jblang/z80ctrl/firmware/emulation/bdos.c

/* z80ctrl (https://github.com/jblang/z80ctrl)
 * Copyright 2018-2023 J.B. Langston
 *
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
 * THE SOFTWARE IS PROVIDED "AS IS", WITHOUT WARRANTY OF ANY KIND, EXPRESS OR
 * IMPLIED, INCLUDING BUT NOT LIMITED TO THE WARRANTIES OF MERCHANTABILITY,
 * FITNESS FOR A PARTICULAR PURPOSE AND NONINFRINGEMENT. IN NO EVENT SHALL THE
 * AUTHORS OR COPYRIGHT HOLDERS BE LIABLE FOR ANY CLAIM, DAMAGES OR OTHER
 * LIABILITY, WHETHER IN AN ACTION OF CONTRACT, TORT OR OTHERWISE, ARISING
 * FROM, OUT OF OR IN CONNECTION WITH THE SOFTWARE OR THE USE OR OTHER
 * DEALINGS IN THE SOFTWARE.
 */

/*
 * Credit to RunCPM https://github.com/MockbaTheBorg/RunCPM for showing me
 * that emulating BDOS on a FAT filesystem was possible, and for serving as
 * a sanity check to help me understand BDOS behavior when I wasn't sure
 * from reading the BDOS assembly code.  No code has been copied though.
 */

/**
 * @file bdos.c BDOS disk emulation on FatFS
 */

#include <ctype.h>
#include <stdint.h>
#include <stdio.h>
#include <string.h>

#include "fatfs/ff.h"

#include "hardware/io.h"
#include "hardware/memory.h"
#include "hardware/timer.h"

#include "util/ffwrap.h"
#include "util/pgmspace.h"
#include "util/string.h"

#include "bdos.h"

// Uncomment for debug messages

// CP/M constants
#define RECSIZ 128L // # of bytes in a record (rc)
#define RECCNT 128L // Max # of records in an extent
#define EXTSIZ (RECSIZ * RECCNT) // # of bytes in an extent (ex)
#define EXTCNT 32L // Max # of extents in a module
#define MODSIZ (EXTSIZ * EXTCNT) // # of bytes in a module (s2)
#define MODCNT 16L // Max # of modules in a file
#define DEFFCB 0x5c // Default FCB location
#define DEFDMA 0x80 // Default DMA buffer

// BDOS function calls
enum {
    P_TERMCPM = 0,
    C_READ = 1,
    C_WRITE = 2,
    A_READ = 3,
    A_WRITE = 4,
    L_WRITE = 5,
    C_RAWIO = 6,
    C_GETIOB = 7,
    C_SETIOB = 8,
    C_WRITESTR = 9,
    C_READSTR = 10,
    C_STAT = 11,
    S_BDOSVER = 12,
    DRV_ALLRESET = 13,
    DRV_SET = 14,
    F_OPEN = 15,
    F_CLOSE = 16,
    F_SFIRST = 17,
    F_SNEXT = 18,
    F_DELETE = 19,
    F_READ = 20,
    F_WRITE = 21,
    F_MAKE = 22,
    F_RENAME = 23,
    DRV_LOGINVEC = 24,
    DRV_GET = 25,
    F_DMAOFF = 26,
    DRV_ALLOCVEC = 27,
    DRV_SETRO = 28,
    DRV_ROVEC = 29,
    F_ATTRIB = 30,
    DRV_DPB = 31,
    F_USERNUM = 32,
    F_READRAND = 33,
    F_WRITERAND = 34,
    F_SIZE = 35,
    F_RANDREC = 36,
    DRV_RESET = 37,
    DRV_ACCESS = 38,
    DRV_FREE = 39,
    F_WRITEZF = 40
};

const char bdos_names[] PROGMEM =
    "P_TERMCPM\0"
    "C_READ\0"
    "C_WRITE\0"
    "A_READ\0"
    "A_WRITE\0"
    "L_WRITE\0"
    "C_RAWIO\0"
    "C_GETIOB\0"
    "C_SETIOB\0"
    "C_WRITESTR\0"
    "C_READSTR\0"
    "C_STAT\0"
    "S_BDOSVER\0"
    "DRV_ALLRESET\0"
    "DRV_SET\0"
    "F_OPEN\0"
    "F_CLOSE\0"
    "F_SFIRST\0"
    "F_SNEXT\0"
    "F_DELETE\0"
    "F_READ\0"
    "F_WRITE\0"
    "F_MAKE\0"
    "F_RENAME\0"
    "DRV_LOGINVEC\0"
    "DRV_GET\0"
    "F_DMAOFF\0"
    "DRV_ALLOCVEC\0"
    "DRV_SETRO\0"
    "DRV_ROVEC\0"
    "F_ATTRIB\0"
    "DRV_DPB\0"
    "F_USERNUM\0"
    "F_READRAND\0"
    "F_WRITERAND\0"
    "F_SIZE\0"
    "F_RANDREC\0"
    "DRV_RESET\0"
    "DRV_ACCESS\0"
    "DRV_FREE\0"
    "F_WRITEZF\0";

// BDOS return codes
enum {
    BDOS_SUCCESS = 0,
    BDOS_EOF = 1,
    BDOS_ERROR = 0xff
};

// FCB layout
typedef struct {
    uint8_t dr;
    uint8_t fn[11];
    uint8_t ex;
    uint8_t s1;
    uint8_t s2;
    uint8_t rc;
    uint8_t al[16];
    uint8_t cr;
    uint8_t r0, r1, r2;
} fcb_t;

typedef struct {
    uint8_t uu;
    uint8_t fn[11];
    uint8_t ex;
    uint8_t s1;
    uint8_t s2;
    uint8_t rc;
    uint16_t al[8];
} dir_t;

// Disk Parameter Block
typedef struct {
    uint16_t spt;
    uint8_t bsh;
    uint8_t blm;
    uint8_t exm;
    uint16_t dsm;
    uint16_t drm;
    uint8_t al0;
    uint8_t al1;
    uint16_t cks;
    uint16_t off;
} dpb_t;

// Parameter mailbox format
typedef struct {
    uint16_t fcbaddr;
    uint16_t ret;
    uint8_t curdrv;
    uint16_t dmaaddr;
    uint8_t usernum;
    uint16_t alloc;
    uint16_t rodsk;
    uint16_t dlog;
} bdos_mailbox_t;

static uint16_t dma_mailbox = 0;
static uint8_t dma_command = 0;
static dma_status_t dma_status = DMA_MAILBOX_UNSET;
static bdos_mailbox_t params;

uint8_t curfn[11]; // FCB filename of the currently open file
static fcb_t curfcb; // FCB for the current command
static FIL curfil;
static FILINFO curfno;

uint8_t bdos_debug = 0;

/**
 * Get null-terminated filename.ext from fixed length FCB field
 */
void fcb_fatname(uint8_t* fatname, uint8_t* fcbname)
{
    uint8_t j = 0;
    for (uint8_t i = 0; i < 11; i++) {
        if (i == 8)
            fatname[j++] = '.';
        if (fcbname[i] != ' ')
            fatname[j++] = toupper(fcbname[i] & 0x7f);
    }
    fatname[j] = '\0';
}

/**
 * Set fixed-length FCB field from null-terminated filename.ext
 */
void fcb_setname(uint8_t* fcbname, uint8_t* fatname)
{
    uint8_t i = 0, j = 0;
    while (i < 8)
        if (fatname[j] == '.' || fatname[j] == 0)
            fcbname[i++] = ' ';
        else if (fatname[j] == '*')
            fcbname[i++] = '?';
        else
            fcbname[i++] = toupper(fatname[j++] & 0x7f);
    while (fatname[j] == '*' || fatname[j] == '.')
        j++;
    while (i < 11)
        if (fatname[j] == 0)
            fcbname[i++] = ' ';
        else if (fatname[j] == '*')
            fcbname[i++] = '?';
        else
            fcbname[i++] = toupper(fatname[j++] & 0x7f);
}

/**
 * Parse d:filename.ext argument and set FCB fields
 */
void fcb_setdrivename(uint8_t* drive, uint8_t* filename, char* arg)
{
    if (arg[1] == ':') {
        if (arg[0] >= 'a' && arg[0] <= 'p')
            *drive = arg[0] - 'a' + 1;
        else if (arg[0] >= 'A' && arg[0] <= 'P')
            *drive = arg[0] - 'A' + 1;
        else
            *drive = 0;
        fcb_setname(filename, arg + 2);
    } else {
        fcb_setname(filename, arg);
    }
}

/**
 * Calculate a 32-bit offset from random fields in FCB
 */
uint32_t fcb_randoffset(fcb_t* f)
{
    return (((uint32_t)f->r2 << 16) | (f->r1 << 8) | f->r0) * RECSIZ;
}

/**
 * Calculate a 32-bit offset from sequential fields in FCB
 */
uint32_t fcb_seqoffset(fcb_t* f)
{
    return f->s2 * MODSIZ + f->ex * EXTSIZ + f->cr * RECSIZ;
}

/**
 * Set sequential fields in FCB from 32-bit offset
 */
void fcb_setseq(fcb_t* f, uint32_t offset)
{
    f->cr = (offset / RECSIZ) % RECCNT;
    f->ex = (offset / EXTSIZ) % EXTCNT;
    f->s2 = (offset / MODSIZ) % MODCNT;
}

/**
 * Set random fields in FCB from 32-bit offset
 */
uint32_t fcb_setrand(fcb_t* f, uint32_t offset)
{
    f->r0 = offset & 0xff;
    f->r1 = (offset >> 8) & 0xff;
    f->r2 = (offset >> 16) & 0xff;
}

/**
 * Check whether file matches mask using CP/M wildcard rules
 */
uint8_t fcb_match(uint8_t* mask, uint8_t* fcbname)
{
    for (uint8_t i = 0; i < 11; i++)
        if (mask[i] != '?' && toupper(mask[i]) != toupper(fcbname[i]))
            return 0;
    return 1;
}

/**
 * Print the filename from an FCB
 */
uint8_t fcb_printfn(uint8_t* fn)
{
    for (uint8_t i = 0; i < 11; i++) {
        if (i == 8)
            putchar(' ');
        if (0x20 <= (fn[i] & 0x7f) && (fn[i] & 0x7f) <= 0x7e)
            putchar(fn[i] & 0x7f);
        else
            putchar(' ');
    }
}

/**
 * Print the FAT filename from an FCB
 */
uint8_t fcb_printfatfn(uint8_t* fn)
{
    for (uint8_t i = 0; i < 12; i++) {
        if (fn[i] == 0) {
            while (i++ < 12)
                putchar(' ');
            break;
        }
        if (fn[i] >= 20)
            putchar(fn[i]);
        else
            putchar(' ');
    }
}

/**
 * Dump the contents of an FCB
 */
uint8_t fcb_dump(fcb_t* f)
{
    printf_P(PSTR("dr filename ext   cr ex s2   r0 r1 r2   rc s1\n"));
    printf_P(PSTR("%02x "), f->dr);
    fcb_printfn(f->fn);
    printf_P(PSTR("   %02x %02x %02x"), f->cr, f->ex, f->s2);
    printf_P(PSTR("   %02x %02x %02x"), f->r0, f->r1, f->r2);
    printf_P(PSTR("   %02x %02x\n"), f->rc, f->s1);
}

/**
 * Dump the contents of a directory entry
 */
uint8_t dir_dump(dir_t* d)
{
    printf_P(PSTR("uu filename ext   ex s2   rc s1   alloc\n"));
    printf_P(PSTR("%02x "), d->uu);
    fcb_printfn(d->fn);
    printf_P(PSTR("   %02x %02x"), d->ex, d->s2);
    printf_P(PSTR("   %02x %02x   "), d->rc, d->s1);
    for (uint8_t i = 0; i < 8; i++)
        printf_P(PSTR("%04x "), d->al[i]);
    putchar('\n');
}

/**
 * Log the current command and parameters
 */
void bdos_log(const char* message)
{
    printf_P(PSTR("\n%S: BDOS %d %S   fcb %04xh   dma %04xh   ret %02x\n"), message, dma_command, skip_strings(bdos_names, dma_command), params.fcbaddr, params.dmaaddr, params.ret);
    if (dma_command != F_SNEXT && dma_command != P_TERMCPM)
        fcb_dump(&curfcb);
}

/**
 * Translate FatFS error to BDOS error and log error if appropriate
 */
uint8_t bdos_error(FRESULT fr)
{
    if (fr == FR_OK) {
        return BDOS_SUCCESS;
    } else {
        bdos_log(PSTR("Error"));
        printf_P(PSTR("FatFs error %d: %S\n"), fr, ffw_error(fr));
        return BDOS_ERROR;
    }
}

/**
 * Search for a files matching name in an FCB
 */
uint8_t bdos_search(uint8_t mode)
{
    static dir_t dirfcb; // Directory entry returned by the last search command
    static uint8_t mask[12];
    static uint8_t searchex;
    static uint32_t bytesleft;
    static uint16_t blockno;
    static DIR dir;
    FRESULT fr;
    uint8_t buf[RECSIZ];

    // On first search, save mask and extent, then reopen directory
    if (mode == F_SFIRST) {
        memcpy(mask, curfcb.fn, 11);
        mask[11] = 0;
        searchex = curfcb.ex;
        f_closedir(&dir);
        if (fr = f_opendir(&dir, ".") != FR_OK)
            return bdos_error(fr);
        memset(&dirfcb, 0, sizeof(dir_t));
        bytesleft = 0;
        blockno = 1;
    }

    // Get the next file if done with current file
    if (bytesleft == 0) {
        do {
            do {
                if (fr = f_readdir(&dir, &curfno) != FR_OK)
                    return bdos_error(fr);
                if (curfno.fname[0] == 0) // indicate end of directory
                    return BDOS_ERROR;
            } while (curfno.fattrib & AM_DIR); // skip directories
            fcb_setname(dirfcb.fn, curfno.fname);
        } while (!fcb_match(mask, dirfcb.fn)); // check filename match

        // Translate attributes
        if (curfno.fattrib & AM_RDO)
            dirfcb.fn[9] |= 0x80;
        if (curfno.fattrib & AM_SYS || curfno.fattrib & AM_HID)
            dirfcb.fn[10] |= 0x80;
        bytesleft = curfno.fsize;

        if (searchex == '?') {
            // Start at zero if all extents requested
            dirfcb.ex = 0;
        } else {
            // Return specific extent if requested
            dirfcb.ex = searchex;
        }
        dirfcb.s2 = 0;
    } else {
        // Increment extent number
        dirfcb.ex++;
        if (dirfcb.ex >= EXTCNT) {
            dirfcb.ex = 0;
            dirfcb.s2++;
        }
    }

    // Calculate the record count in this extent
    dirfcb.rc = (bytesleft + RECSIZ - 1) / RECSIZ;
    if (dirfcb.rc > RECSIZ)
        dirfcb.rc = RECSIZ;

    // Set the appropriate number of allocated blocks
    uint8_t blocks = (dirfcb.rc + 31) / 32;
    for (uint8_t i = 0; i < 8; i++) {
        if (blocks > 0) {
            dirfcb.al[i] = blockno++;
            blocks--;
        } else {
            dirfcb.al[i] = 0;
        }
    }

    // Check if more extents to return, and decrement bytes left by one extent
    if (bytesleft > EXTSIZ && searchex == '?')
        bytesleft -= EXTSIZ;
    else
        bytesleft = 0;

    if (bdos_debug) {
        printf_P(PSTR("Directory Entry:\n"));
        dir_dump(&dirfcb);
    }

    // Only write directory entry to dma buffer for actual search command
    if (dma_command == F_SFIRST || dma_command == F_SNEXT) {
        // Pad extra space with empty directory entries
        memcpy(buf, &dirfcb, sizeof(dir_t));
        memset(buf + sizeof(dir_t), 0xe5, RECSIZ - sizeof(dir_t));
        // Save directory entry to DMA buffer
        mem_write(params.dmaaddr, buf, RECSIZ);
    }
    return BDOS_SUCCESS;
}

/**
 * Open the FAT file needed by the FCB if it's not already
 */
FRESULT fcb_openfil(fcb_t* fcb, uint8_t mode)
{
    uint8_t fatfn[13];
    fcb_fatname(fatfn, fcb->fn);
    if (strncmp(fcb->fn, curfn, 11) != 0) {
        f_close(&curfil);
        strncpy(curfn, fcb->fn, 11);
        FRESULT fr = f_open(&curfil, fatfn, mode);
    } else {
        return FR_OK;
    }
}

/**
 * Open file named in FCB
 */
uint8_t bdos_open()
{
    FRESULT fr;

    // Handle read-only files
    uint8_t mode = FA_READ;
    if (!(curfno.fattrib & AM_RDO))
        mode |= FA_WRITE;

    // Command-specific behavior
    if (dma_command == F_OPEN) {
        // Search for first existing file to match any wildcards
        if (bdos_search(F_SFIRST) != BDOS_SUCCESS)
            return BDOS_ERROR;
        curfcb.s2 = 0; // s2 is always zeroed by open call
    } else {
        // Otherwise make a new file
        mode |= FA_CREATE_NEW;
        // New files start at offset 0
        fcb_setseq(&curfcb, 0);
    }

    // Open the file
    if ((fr = fcb_openfil(&curfcb, mode)) != FR_OK)
        return bdos_error(fr);

    // Write back FCB except for random fields
    mem_write(params.fcbaddr, &curfcb, sizeof(fcb_t) - 3);
    return BDOS_SUCCESS;
}

/**
 * Close file associated with fcb
 */
uint8_t bdos_close()
{
    f_close(&curfil);
    // Clear currently open filename
    memset(curfn, 0, 11);
    // Write back FCB except for random fields
    mem_write(params.fcbaddr, &curfcb, sizeof(fcb_t) - 3);
    return BDOS_SUCCESS;
}

/**
 * Read or write the file associated with the FCB
 */
uint8_t bdos_readwrite()
{
    uint32_t offset;
    uint8_t buf[RECSIZ];
    FRESULT fr;
    UINT br;

    // Try to get an active FP for this FCB
    if ((fr = fcb_openfil(&curfcb, FA_READ | FA_WRITE)) != FR_OK)
        return bdos_error(fr);
    // Calculate offset for access method
    if (dma_command == F_READ || dma_command == F_WRITE) {
        offset = fcb_seqoffset(&curfcb);
    } else {
        offset = fcb_randoffset(&curfcb);
    }
    // Don't seek past EOF when reading
    if (offset >= f_size(&curfil) && (dma_command == F_READ || dma_command == F_READRAND))
        return BDOS_EOF;
    // Seek to calculated offset if different from current offset
    if (offset != f_tell(&curfil))
        if ((fr = f_lseek(&curfil, offset)) != FR_OK)
            return bdos_error(fr);
    // Do the read or write operation
    if (dma_command == F_READRAND || dma_command == F_READ) {
        if ((fr = f_read(&curfil, buf, RECSIZ, &br)) != FR_OK)
            return bdos_error(fr);
        // pad incomplete record with 0
        memset(buf + br, 0x0, RECSIZ - br);
        mem_write(params.dmaaddr, buf, RECSIZ);
    } else {
        mem_read(params.dmaaddr, buf, RECSIZ);
        if ((fr = f_write(&curfil, buf, RECSIZ, &br)) != FR_OK)
            return bdos_error(fr);
    }
    // Automatically increment record if in sequential mode
    if (dma_command == F_READ || dma_command == F_WRITE)
        offset += RECSIZ;
    fcb_setseq(&curfcb, offset);
    // Write back FCB except for random fields
    mem_write(params.fcbaddr, &curfcb, sizeof(fcb_t) - 3);
    // Indicate success
    return 0;
}

/**
 * Update random fields in FCB from sequential fields
 */
uint8_t bdos_randrec()
{
    fcb_setrand(&curfcb, (fcb_seqoffset(&curfcb) + RECSIZ - 1) / RECSIZ);
    mem_write(params.fcbaddr, &curfcb, sizeof(fcb_t));
    return 0;
}

/**
 * Delete file named in FCB
 */
uint8_t bdos_delete()
{
    FRESULT fr = FR_OK;
    // Search for files matching wildcards
    uint8_t ret = bdos_search(F_SFIRST);
    while (!ret) {
        if (fr = f_unlink(curfno.fname) != FR_OK)
            return bdos_error(fr);
        ret = bdos_search(F_SNEXT);
    }
    return bdos_error(fr);
}

/**
 * Rename file named in fCB
 */
uint8_t bdos_rename()
{
    uint8_t old[13], new[13];
    fcb_fatname(old, curfcb.fn);
    fcb_fatname(new, curfcb.al + 1);
    return bdos_error(f_rename(old, new));
}

/**
 * Compute file size
 */
uint8_t bdos_size()
{
    uint8_t ret;
    if (ret = bdos_search(F_SFIRST))
        return ret;
    fcb_setrand(&curfcb, (curfno.fsize + RECSIZ - 1) / RECSIZ);
    mem_write(params.fcbaddr, &curfcb, sizeof(fcb_t));
}

/**
 * Close any files left open
 */
uint8_t bdos_terminate()
{
    memset(curfn, 0, 11);
    f_close(&curfil);
}

/**
 * Emulate a BDOS curdrv function using DMA
 */
void bdos_dma_execute()
{
    // Get DMA parameters
    mem_read(dma_mailbox, &params, sizeof(bdos_mailbox_t));

    // Get the specified FCB
    if (dma_command != F_SNEXT) {
        mem_read(params.fcbaddr, &curfcb, sizeof(fcb_t));
    }
    if (bdos_debug)
        bdos_log(PSTR("Before"));

    switch (dma_command) {
    case P_TERMCPM:
        params.ret = bdos_terminate();
        break;
    case F_OPEN:
    case F_MAKE:
        params.ret = bdos_open();
        break;
    case F_CLOSE:
        params.ret = bdos_close();
        break;
    case F_SFIRST:
    case F_SNEXT:
        params.ret = bdos_search(dma_command);
        break;
    case F_READ:
    case F_WRITE:
    case F_READRAND:
    case F_WRITERAND:
    case F_WRITEZF:
        params.ret = bdos_readwrite();
        break;
    case F_DELETE:
        params.ret = bdos_delete();
        break;
    case F_RENAME:
        params.ret = bdos_rename();
        break;
    case F_ATTRIB:
        break; // currently unimplemented
    case F_SIZE:
        params.ret = bdos_size();
        break;
    case F_RANDREC:
        params.ret = bdos_randrec();
        break;
    default:
        params.ret = bdos_error(FR_INVALID_PARAMETER);
        break;
    }
    if (bdos_debug)
        bdos_log(PSTR("After"));

    // Write back return values
    mem_write(dma_mailbox, &params, sizeof(bdos_mailbox_t));
}

/**
 * Initialize default FCB and command tail
 */
void bdos_init(int argc, char* argv[])
{
    char comtail[256];
    fcb_t deffcb;

    // Set up default FCB with filenames on command line
    memset(&deffcb, 0, sizeof(fcb_t));
    if (argc >= 2)
        fcb_setdrivename(&deffcb.dr, deffcb.fn, argv[1]);
    else
        memset(deffcb.fn, ' ', 11);
    if (argc >= 3)
        fcb_setdrivename(deffcb.al, deffcb.al + 1, argv[2]);
    else
        memset(deffcb.al + 1, ' ', 11);
    mem_write(DEFFCB, &deffcb, sizeof(fcb_t));
    memset(comtail, ' ', 256);

    // Save the entire command line tail to DMA buffer
    char* next = comtail + 1;
    for (int i = 1; i < argc; i++) {
        strcpy(next, argv[i]);
        next += strlen(argv[i]);
        *next++ = ' ';
    }
    comtail[0] = (uint8_t)(next - comtail - 1);
    mem_write(DEFDMA, comtail, RECSIZ);
}

/**
 * Reset the DMA parameter address
 */
uint8_t bdos_dma_reset()
{
    dma_function = NULL;
    dma_status = DMA_MAILBOX_UNSET;
    dma_mailbox = 0;
    return 0xa5;
}

/**
 * Queue a DMA command for execution
 */
void bdos_dma_command(uint8_t data)
{
    switch (dma_status) {
    case DMA_MAILBOX_UNSET:
        dma_mailbox = data;
        dma_status = DMA_MAILBOX_HALFSET;
        break;
    case DMA_MAILBOX_HALFSET:
        dma_mailbox |= (data << 8);
        dma_status = DMA_MAILBOX_SET;
        break;
    case DMA_MAILBOX_SET:
        dma_command = data;
        dma_function = bdos_dma_execute;
        break;
    default:
        dma_function = NULL;
    }
}
