jblang/z80ctrl/firmware/util/ffwrap.c

/* z80ctrl (https://github.com/jblang/z80ctrl)
 * Copyright 2018-2023 J.B. Langston
 *
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
 * THE SOFTWARE IS PROVIDED "AS IS", WITHOUT WARRANTY OF ANY KIND, EXPRESS OR
 * IMPLIED, INCLUDING BUT NOT LIMITED TO THE WARRANTIES OF MERCHANTABILITY,
 * FITNESS FOR A PARTICULAR PURPOSE AND NONINFRINGEMENT. IN NO EVENT SHALL THE
 * AUTHORS OR COPYRIGHT HOLDERS BE LIABLE FOR ANY CLAIM, DAMAGES OR OTHER
 * LIABILITY, WHETHER IN AN ACTION OF CONTRACT, TORT OR OTHERWISE, ARISING
 * FROM, OUT OF OR IN CONNECTION WITH THE SOFTWARE OR THE USE OR OTHER
 * DEALINGS IN THE SOFTWARE.
 */

/**
 * @file ffwrap.c Wrapper functions for FatFS
 */

#include <stdint.h>
#include <stdio.h>
#include <string.h>

#include "fatfs/ff.h"

#include "hardware/memory.h"
#include "hardware/tms9918.h"

#include "util/pgmspace.h"

#include "ffwrap.h"
#include "string.h"

/*-----------------------------------------------------------------------*/
/* Copy a File/Directory                                                 */
/*-----------------------------------------------------------------------*/

FRESULT f_copy(
    const TCHAR* src, /* Pointer to the source file */
    const TCHAR* dst /* Pointer to the dest file */
)
{
    FIL fsrc, fdst; /* File objects */
    BYTE buffer[FF_MAX_SS]; /* File copy buffer */
    FRESULT fr; /* FatFs function common result code */
    UINT br, bw; /* File read/write count */

    /* Open source file on the drive 1 */
    fr = f_open(&fsrc, src, FA_READ);
    if (fr)
        return fr;

    /* Create destination file on the drive 0 */
    fr = f_open(&fdst, dst, FA_WRITE | FA_CREATE_NEW);
    if (fr)
        return fr;

    /* Copy source to destination */
    for (;;) {
        fr = f_read(&fsrc, buffer, sizeof buffer, &br); /* Read a chunk of source file */
        if (fr || br == 0)
            break; /* error or eof */
        fr = f_write(&fdst, buffer, br, &bw); /* Write it to the destination file */
        if (fr || bw < br)
            break; /* error or disk full */
    }

    /* Close open files */
    f_close(&fsrc);
    f_close(&fdst);

    return fr;
}

char* ffw_splitpath(const char* path)
{
    char* fs = strrchr(path, '/');
    char* bs = strrchr(path, '\\');
    if (fs > bs) {
        *fs = '\0';
        return fs + 1;
    } else if (bs != NULL) {
        *bs = '\0';
        return bs + 1;
    }
    return NULL;
}

/**
 * FatFS wrapper to write a single byte to a file, used by stdio library
 */
int fatfs_putchar(char c, FILE* stream)
{
    FIL* fil = stream->udata;
    if (f_write(fil, &c, 1, NULL) != FR_OK)
        return EOF;
    else
        return 0;
}

/**
 * FatFS wrapper to read a single byte from a file, used by stdio library
 */
int fatfs_getchar(FILE* stream)
{
    FIL* fil = stream->udata;
    char c;

    if (f_read(fil, &c, 1, NULL) == FR_OK)
        return c;
    else
        return EOF;
}

FRESULT ffw_open(FIL* fil, FILE* file, const TCHAR* filename, BYTE mode)
{
    FRESULT fr;
    if ((fr = f_open(fil, filename, mode)) != FR_OK) {
        printf_P(PSTR("error opening '%s': %S\n"), filename, ffw_error(fr));
    } else if (file != NULL) {
        fdev_setup_stream(file, fatfs_putchar, fatfs_getchar, _FDEV_SETUP_RW);
        fdev_set_udata(file, fil);
    }
    return fr;
}

FRESULT ffw_close(FIL* fil)
{
    FRESULT fr;
    if ((fr = f_close(fil)) != FR_OK) {
        printf_P(PSTR("error closing file: %S\n"), ffw_error(fr));
    }
    return fr;
}

FRESULT ffw_read(FIL* fil, void* buff, UINT btr, UINT* br)
{
    FRESULT fr;
    if ((fr = f_read(fil, buff, btr, br)) != FR_OK)
        printf_P(PSTR("error reading file: %S\n"), ffw_error(fr));
    return fr;
}

FRESULT ffw_write(FIL* fil, void* buff, UINT btw, UINT* bw)
{
    FRESULT fr;
    if ((fr = f_write(fil, buff, btw, bw)) != FR_OK)
        printf_P(PSTR("error writing file: %S\n"), ffw_error(fr));
    return fr;
}

FRESULT ffw_seek(FIL* fil, FSIZE_t ofs)
{
    FRESULT fr;
    if ((fr = f_lseek(fil, ofs)) != FR_OK)
        printf_P(PSTR("error seeking file: %S\n"), ffw_error(fr));
    return fr;
}

FRESULT ffw_delete(const TCHAR* path, const TCHAR* dummy)
{
    FRESULT fr;
    if ((fr = f_unlink(path)) != FR_OK)
        printf_P(PSTR("error deleting '%s': %S\n"), path, ffw_error(fr));
    return fr;
}

FRESULT ffw_rename(const TCHAR* path_old, const TCHAR* path_new)
{
    FRESULT fr;
    if ((fr = f_rename(path_old, path_new)) != FR_OK)
        printf_P(PSTR("error renaming '%s' to '%s': %S\n"), path_old, path_new, ffw_error(fr));
    return fr;
}

FRESULT ffw_copy(const TCHAR* path_old, const TCHAR* path_new)
{
    FRESULT fr;
    if ((fr = f_copy(path_old, path_new)) != FR_OK)
        printf_P(PSTR("error copying '%s' to '%s': %S\n"), path_old, path_new, ffw_error(fr));
    return fr;
}

void ffw_iterate(operation_t operation, int count, char* file[], char* dest)
{
    FRESULT fr;
    DIR dir;
    FILINFO fno;
    char srcpath[128], destpath[128];

    uint8_t dest_is_dir = dest != NULL && f_stat(dest, &fno) == FR_OK && fno.fattrib & AM_DIR;
    for (uint8_t i = 0; i < count; i++) {
        const char* path1 = file[i];
        const char* path2 = ffw_splitpath(file[i]);
        if (path2 == NULL)
            fr = f_findfirst(&dir, &fno, ".", path1);
        else
            fr = f_findfirst(&dir, &fno, path1, path2);

        while (fr == FR_OK && fno.fname[0] != 0) {
            if (path2 != NULL) {
                strcpy(srcpath, path1);
                strcat_P(srcpath, PSTR("/"));
                strcat(srcpath, fno.fname);
            } else {
                strcpy(srcpath, fno.fname);
            }
            if (dest != NULL) {
                strcpy(destpath, dest);
                if (dest_is_dir) {
                    strcat_P(destpath, PSTR("/"));
                    strcat(destpath, fno.fname);
                }
            }
            operation(srcpath, destpath);
            fr = f_findnext(&dir, &fno);
        }
        fr = f_closedir(&dir);
    }
    if (fr != FR_OK)
        printf_P(PSTR("error enumerating files: %S\n"), ffw_error(fr));
}

const char fr_text[] PROGMEM = 
    "OK\0"                      // FR_OK
    "disk error\0"              // FR_DISK_ERR
    "internal error\0"          // FR_INT_ERR
    "drive not ready\0"         // FR_NOT_READY
    "file not found\0"          // FR_NO_FILE
    "path not found\0"          // FR_NO_PATH
    "invalid path name\0"       // FR_INVALID_NAME
    "access denied\0"           // FR_DENIED
    "file already exists\0"     // FR_EXIST
    "invalid object\0"          // FR_INVALID_OBJECT
    "write protected\0"         // FR_WRITE_PROTECTED
    "invalid drive number\0"    // FR_INVALID_DRIVE
    "drive not mounted\0"       // FR_NOT_ENABLED
    "invalid filesystem\0"      // FR_NO_FILESYSTEM
    "mkfs aborted\0"            // FR_MKFS_ABORTED
    "timeout\0"                 // FR_TIMEOUT
    "file locked\0"             // FR_LOCKED
    "out of memory\0"           // FR_NOT_ENOUGH_CORE
    "too many open files\0"     // FR_TOO_MANY_OPEN_FILES
    "invalid parameter\0";      // FR_INVALID_PARAMETER

const char* ffw_error(FRESULT fr)
{
    return skip_strings(fr_text, fr);
}

void ffw_init()
{
    static FATFS fs;
    FRESULT fr;
    if ((fr = f_mount(&fs, "", 1)) != FR_OK)
        printf_P(PSTR("error mounting drive: %S\n"), skip_strings(fr_text, fr));
}
