jblang/z80ctrl/examples/filedma.asm

; z80ctrl (https://github.com/jblang/z80ctrl)
; Copyright 2018 J.B. Langston
;
; Permission is hereby granted, free of charge, to any person obtaining a 
; copy of this software and associated documentation files (the "Software"), 
; to deal in the Software without restriction, including without limitation 
; the rights to use, copy, modify, merge, publish, distribute, sublicense, 
; and/or sell copies of the Software, and to permit persons to whom the 
; Software is furnished to do so, subject to the following conditions:
; 
; The above copyright notice and this permission notice shall be included in
; all copies or substantial portions of the Software.
; 
; THE SOFTWARE IS PROVIDED "AS IS", WITHOUT WARRANTY OF ANY KIND, EXPRESS OR
; IMPLIED, INCLUDING BUT NOT LIMITED TO THE WARRANTIES OF MERCHANTABILITY, 
; FITNESS FOR A PARTICULAR PURPOSE AND NONINFRINGEMENT. IN NO EVENT SHALL THE
; AUTHORS OR COPYRIGHT HOLDERS BE LIABLE FOR ANY CLAIM, DAMAGES OR OTHER 
; LIABILITY, WHETHER IN AN ACTION OF CONTRACT, TORT OR OTHERWISE, ARISING 
; FROM, OUT OF OR IN CONNECTION WITH THE SOFTWARE OR THE USE OR OTHER 
; DEALINGS IN THE SOFTWARE.

; File DMA client library

; FatFS commands
F_OPEN                  equ 00h
F_CLOSE                 equ 01h
F_READ                  equ 02h
F_WRITE                 equ 03h
F_LSEEK                 equ 04h
F_TRUNCATE              equ 05h
F_SYNC                  equ 06h
F_FORWARD               equ 07h
F_EXPAND                equ 08h
F_GETS                  equ 09h
F_PUTC                  equ 0ah
F_PUTS                  equ 0bh
F_PRINTF                equ 0ch
F_TELL                  equ 0dh
F_EOF                   equ 0eh
F_SIZE                  equ 0fh
F_ERROR                 equ 10h
F_OPENDIR               equ 11h
F_CLOSEDIR              equ 12h
F_READDIR               equ 13h
F_FINDFIRST             equ 14h
F_FINDNEXT              equ 15h
F_STAT                  equ 16h
F_UNLINK                equ 17h
F_RENAME                equ 18h
F_CHMOD                 equ 19h
F_UTIME                 equ 1ah
F_MKDIR                 equ 1bh
F_CHDIR                 equ 1ch
F_CHDRIVE               equ 1dh
F_GETCWD                equ 1eh
F_MOUNT                 equ 1fh
F_MKFS                  equ 20h
F_FDISK                 equ 21h
F_GETFREE               equ 22h
F_GETLABEL              equ 23h
F_SETLABEL              equ 24h
F_SETCP                 equ 25h
F_DISK_STATUS           equ 26h
F_DISK_INITIALIZE       equ 27h
F_DISK_READ             equ 28h
F_DISK_WRITE            equ 29h
F_DISK_IOCTL            equ 2ah
F_GET_FATTIME           equ 2bh
F_GET_CLIBUF            equ 40h

; FatFS file open flags
FA_READ				    equ 01h
FA_WRITE			    equ 02h
FA_OPEN_EXISTING	    equ 00h
FA_CREATE_NEW		    equ 04h
FA_CREATE_ALWAYS	    equ 08h
FA_OPEN_ALWAYS		    equ 10h
FA_OPEN_APPEND		    equ 30h

; FatFS result codes
FR_OK				    equ 0h
FR_DISK_ERR			    equ 1h
FR_INT_ERR				equ 2h
FR_NOT_READY			equ 3h
FR_NO_FILE				equ 4h
FR_NO_PATH				equ 5h
FR_INVALID_NAME		    equ 6h
FR_DENIED				equ 7h
FR_EXIST				equ 8h
FR_INVALID_OBJECT		equ 9h
FR_WRITE_PROTECTED		equ 0ah
FR_INVALID_DRIVE		equ 0bh
FR_NOT_ENABLED			equ 0ch
FR_NO_FILESYSTEM		equ 0dh
FR_MKFS_ABORTED		    equ 0eh
FR_TIMEOUT				equ 0fh
FR_LOCKED				equ 10h
FR_NOT_ENOUGH_CORE		equ 11h
FR_TOO_MANY_OPEN_FILES	equ 12h
FR_INVALID_PARAMETER	equ 13h

dmaport                 equ 0bh     ; port to initiate dma transfer
fplen                   equ 42      ; length of fatfs file pointer

; error messages corresponding to codes
fr_text:
    db "OK", 0
    db "disk error", 0
    db "internal error", 0
    db "drive not ready", 0
    db "file not found", 0
    db "path not found", 0
    db "invalid path name", 0
    db "access denied", 0
    db "file already exists", 0
    db "invalid object", 0
    db "write protected", 0
    db "invalid drive number", 0
    db "drive not mounted", 0
    db "invalid filesystem", 0
    db "mkfs aborted", 0
    db "timeout", 0
    db "file locked", 0
    db "out of memory", 0
    db "too many open files", 0

; look up error message for error code
;       A = error code
;       returns pointer to string in DE
f_error:
    ld      b,a
    inc     b
    ld      de, fr_text
.loop
    call    f_cli_next
    djnz    .loop
    ret

; set a byte-length parameter
macro f_setb name, value
    ld      a, value
    ld      (name), a
endmacro

; set a word-length parameter
macro f_setw name, value
    ld      hl, value
    ld      (name), hl
endmacro

; copy a word-length parameter
macro f_cpyw dst, src
    ld      hl, (src)
    ld      (dst), hl
endmacro

; call a DMA function
macro f_call func
    ld      a, func
    call    f_dma_exec
endmacro

; get CLI buffer
;   f_outbuf must already be set to buffer address
;   f_maxlen must already be set to buffer length
; returns:
;   A = param count
;   DE = pointer to first CLI param
f_cli_first:
    ld      a, F_GET_CLIBUF
    call    f_dma_exec
    ld      de, (f_outaddr)
    ld      a, (de)
    inc     de
    ret

; point DE to next CLI parameter
;   DE = starting address
;   returns address of next parameter in DE
f_cli_next:
    ex      de, hl
    xor     a
.loop
    cp      (hl)
    inc     hl
    jp      nz, .loop
    ex      de, hl
    ret

; initiate a DMA transfer
;       A = DMA command
;       returns result code in A; NZ set if err
f_dma_exec:
    out     (dmaport), a
    ld      a, (f_result)
    cp      FR_OK
    ret

; set up the mailbox address to use for DMA communication
;       HL = address of mailbox
f_init:
    ld      hl, f_mailbox
    ld      c, dmaport
    in      a, (c)           ; clear DMA mailbox address
    out     (c), l           ; set new DMA mailbox address
    out     (c), h
    ret

; mailbox for DMA communicaation
f_mailbox:
f_fpaddr    dw 0            ; address of file pointer
f_inaddr    dw 0            ; address of input buffer
f_outaddr   dw 0            ; address of output buffer
f_maxlen    dw 0            ; maximum buffer length
f_retlen    dw 0            ; length read or written
f_ofs       dd 0            ; offset for f_lseek
f_mode      db 0            ; f_mode for f_open, attr for f_chmod
f_mask      db 0            ; f_mask for f_chmod
f_result    db 0            ; result of last operation
