jblang/z80ctrl/firmware/emulation/simhboot.h

/*  altairz80_dsk.c: MITS Altair 88-DISK Simulator
    Copyright (c) 2002-2014, Peter Schorn
    Permission is hereby granted, free of charge, to any person obtaining a
    copy of this software and associated documentation files (the "Software"),
    to deal in the Software without restriction, including without limitation
    the rights to use, copy, modify, merge, publish, distribute, sublicense,
    and/or sell copies of the Software, and to permit persons to whom the
    Software is furnished to do so, subject to the following conditions:
    The above copyright notice and this permission notice shall be included in
    all copies or substantial portions of the Software.
    THE SOFTWARE IS PROVIDED "AS IS", WITHOUT WARRANTY OF ANY KIND, EXPRESS OR
    IMPLIED, INCLUDING BUT NOT LIMITED TO THE WARRANTIES OF MERCHANTABILITY,
    FITNESS FOR A PARTICULAR PURPOSE AND NONINFRINGEMENT. IN NO EVENT SHALL
    PETER SCHORN BE LIABLE FOR ANY CLAIM, DAMAGES OR OTHER LIABILITY, WHETHER
    IN AN ACTION OF CONTRACT, TORT OR OTHERWISE, ARISING FROM, OUT OF OR IN
    CONNECTION WITH THE SOFTWARE OR THE USE OR OTHER DEALINGS IN THE SOFTWARE.
    Except as contained in this notice, the name of Peter Schorn shall not
    be used in advertising or otherwise to promote the sale, use or other dealings
    in this Software without prior written authorization from Peter Schorn.
    Based on work by Charles E Owen (c) 1997
*/

/**
 * @file simhboot.h SIMH AltairZ80 bootloader
 *
 * Assembled version of simhboot.asm
 */

#ifndef EMULATION_SIMHBOOT_H
#define EMULATION_SIMHBOOT_H

#include "util/pgmspace.h"

unsigned const char simhboot_bin[] PROGMEM = {
    0xf3, 0x06, 0x80, 0x3e, 0x0e, 0xd3, 0xfe, 0x05, /* ff00-ff07 */
    0xc2, 0x05, 0xff, 0x3e, 0x16, 0xd3, 0xfe, 0x3e, /* ff08-ff0f */
    0x12, 0xd3, 0xfe, 0xdb, 0xfe, 0xb7, 0xca, 0x20, /* ff10-ff17 */
    0xff, 0x3e, 0x0c, 0xd3, 0xfe, 0xaf, 0xd3, 0xfe, /* ff18-ff1f */
    0x21, 0x00, 0x5c, 0x11, 0x33, 0xff, 0x0e, 0x88, /* ff20-ff27 */
    0x1a, 0x77, 0x13, 0x23, 0x0d, 0xc2, 0x28, 0xff, /* ff28-ff2f */
    0xc3, 0x00, 0x5c, 0x31, 0x21, 0x5d, 0x3e, 0x00, /* ff30-ff37 */
    0xd3, 0x08, 0x3e, 0x04, 0xd3, 0x09, 0xc3, 0x19, /* ff38-ff3f */
    0x5c, 0xdb, 0x08, 0xe6, 0x02, 0xc2, 0x0e, 0x5c, /* ff40-ff47 */
    0x3e, 0x02, 0xd3, 0x09, 0xdb, 0x08, 0xe6, 0x40, /* ff48-ff4f */
    0xc2, 0x0e, 0x5c, 0x11, 0x00, 0x00, 0x06, 0x08, /* ff50-ff57 */
    0xc5, 0xd5, 0x11, 0x86, 0x80, 0x21, 0x88, 0x5c, /* ff58-ff5f */
    0xdb, 0x09, 0x1f, 0xda, 0x2d, 0x5c, 0xe6, 0x1f, /* ff60-ff67 */
    0xb8, 0xc2, 0x2d, 0x5c, 0xdb, 0x08, 0xb7, 0xfa, /* ff68-ff6f */
    0x39, 0x5c, 0xdb, 0x0a, 0x77, 0x23, 0x1d, 0xc2, /* ff70-ff77 */
    0x39, 0x5c, 0xd1, 0x21, 0x8b, 0x5c, 0x06, 0x80, /* ff78-ff7f */
    0x7e, 0x12, 0x23, 0x13, 0x05, 0xc2, 0x4d, 0x5c, /* ff80-ff87 */
    0xc1, 0x21, 0x00, 0x5c, 0x7a, 0xbc, 0xc2, 0x60, /* ff88-ff8f */
    0x5c, 0x7b, 0xbd, 0xd2, 0x80, 0x5c, 0x04, 0x04, /* ff90-ff97 */
    0x78, 0xfe, 0x20, 0xda, 0x25, 0x5c, 0x06, 0x01, /* ff98-ff9f */
    0xca, 0x25, 0x5c, 0xdb, 0x08, 0xe6, 0x02, 0xc2, /* ffa0-ffa7 */
    0x70, 0x5c, 0x3e, 0x01, 0xd3, 0x09, 0x06, 0x00, /* ffa8-ffaf */
    0xc3, 0x25, 0x5c, 0x3e, 0x80, 0xd3, 0x08, 0xfb, /* ffb0-ffb7 */
    0xc3, 0x00, 0x00, 0x00, 0x00, 0x00, 0x00, 0x00, /* ffb8-ffbf */
    0x00, 0x00, 0x00, 0x00, 0x00, 0x00, 0x00, 0x00, /* ffc0-ffc7 */
    0x00, 0x00, 0x00, 0x00, 0x00, 0x00, 0x00, 0x00, /* ffc8-ffcf */
    0x00, 0x00, 0x00, 0x00, 0x00, 0x00, 0x00, 0x00, /* ffd0-ffd7 */
    0x00, 0x00, 0x00, 0x00, 0x00, 0x00, 0x00, 0x00, /* ffd8-ffdf */
    0x00, 0x00, 0x00, 0x00, 0x00, 0x00, 0x00, 0x00, /* ffe0-ffe7 */
    0x00, 0x00, 0x00, 0x00, 0x00, 0x00, 0x00, 0x00, /* ffe8-ffef */
    0x00, 0x00, 0x00, 0x00, 0x00, 0x00, 0x00, 0x00, /* fff0-fff7 */
    0x00, 0x00, 0x00, 0x00, 0x00, 0x00, 0x00, 0x00, /* fff8-ffff */
};
unsigned int simhboot_bin_len = 256;

#endif
